VoronDesign/Voron-Legacy/STLs/Gantry/AB Drive Units/[a]_belt_tensioner_x2.stl

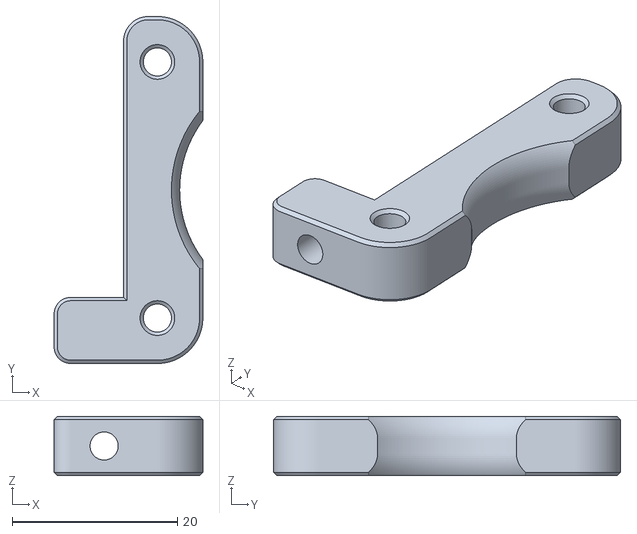
[picture p15: CAD file, 2020-12-23]
STLs/Gantry/AB Drive Units/[a]_belt_tensioner_x2.stl
18.0 x 42.0 x 7.20
