VoronDesign/Voron-Legacy/STLs/Gantry/Front Idlers/front_idler_right_upper.stl

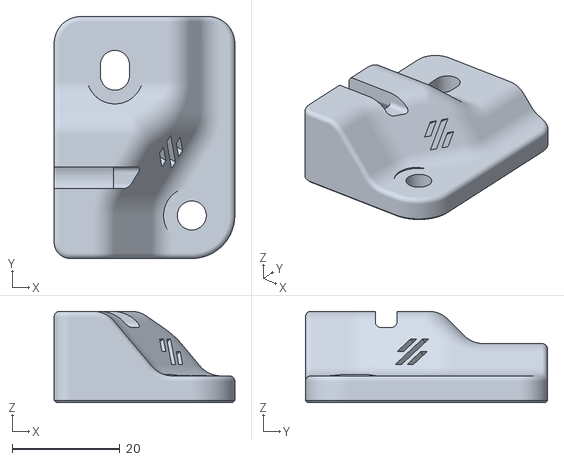
[picture p16: CAD file, 2020-12-23]
STLs/Gantry/Front Idlers/front_idler_right_upper.stl
33.6 x 45.0 x 17.0
