VoronDesign/Voron-Legacy/STLs/Gantry/X Carriage/blower_housing_rear.stl

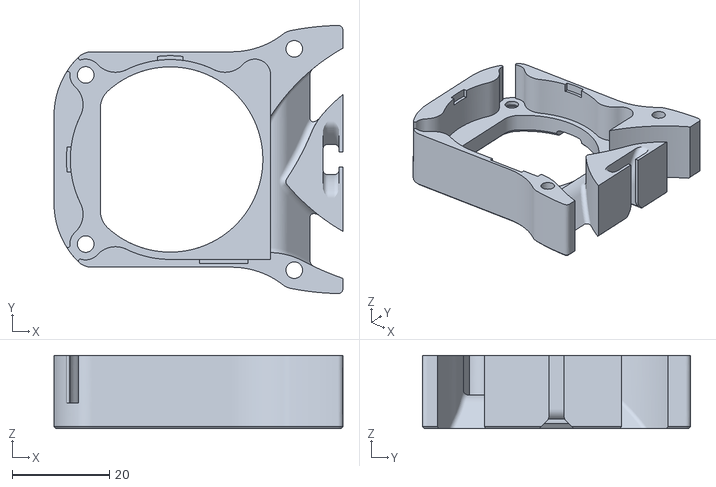
[picture p17: CAD file, 2020-12-30]
STLs/Gantry/X Carriage/blower_housing_rear.stl
59.3 x 55.0 x 15.0
