VoronDesign/Voron-Legacy/STLs/Gantry/X Carriage/Printheads/E3D V6/printhead_front_e3dv6.stl

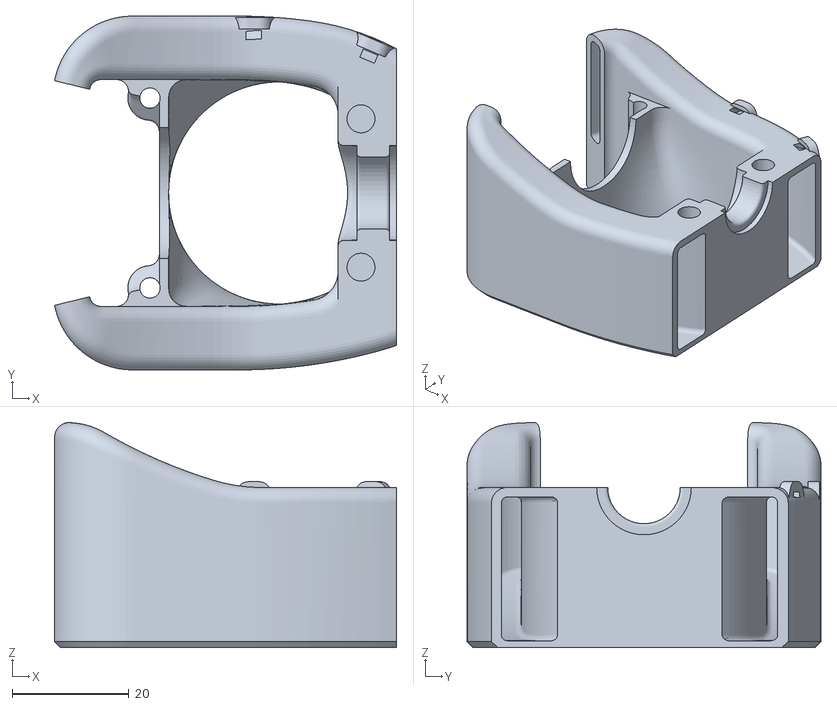
[picture p18: CAD file, 2020-12-23]
STLs/Gantry/X Carriage/Printheads/E3D V6/printhead_front_e3dv6.stl
58.6 x 60.6 x 38.5
