VoronDesign/Voron-Legacy/STLs/Gantry/X Carriage/Printheads/Slice Mosquito/printhead_rear_mosquito.stl

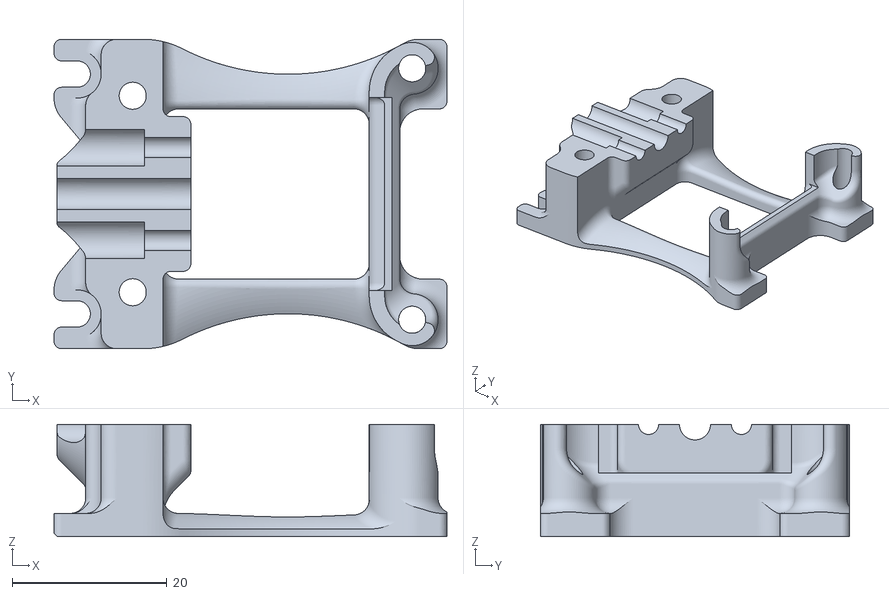
[picture p19: CAD file, 2020-12-23]
STLs/Gantry/X Carriage/Printheads/Slice Mosquito/printhead_rear_mosquito.stl
50.8 x 40.0 x 14.5
