VoronDesign/Voron-Legacy/STLs/Gantry/X Carriage/Printheads/TriangleLab Dragon/printhead_rear_dragon.stl

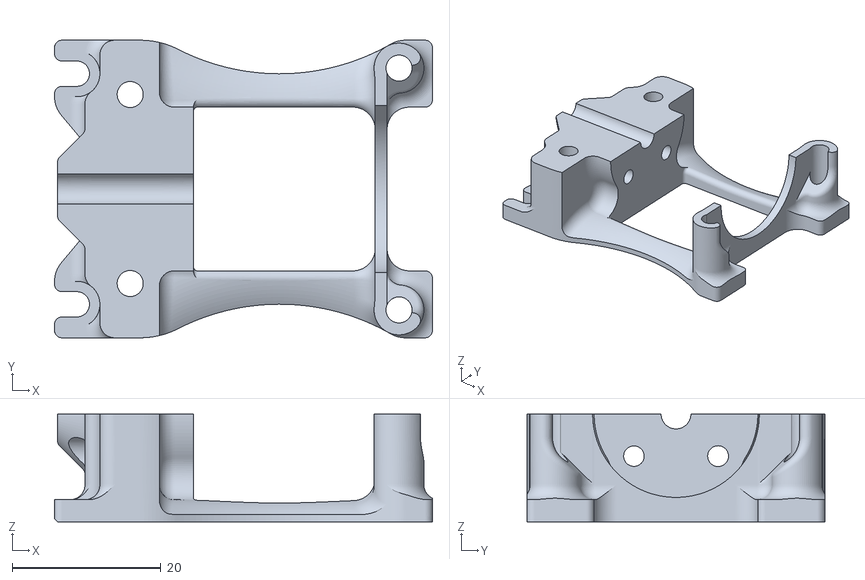
[picture p20: CAD file, 2020-12-23]
STLs/Gantry/X Carriage/Printheads/TriangleLab Dragon/printhead_rear_dragon.stl
50.8 x 40.0 x 14.5
