VoronDesign/Voron-Legacy/STLs/Gantry/XY Joints/y_bearing_retainer_front_x2.stl

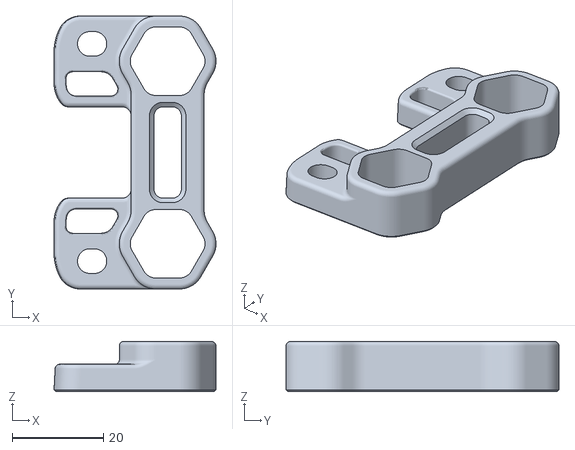
[picture p21: CAD file, 2020-12-23]
STLs/Gantry/XY Joints/y_bearing_retainer_front_x2.stl
35.5 x 59.8 x 11.0
