VoronDesign/Voron-Legacy/STLs/Tools/z_component_alignment_jig.stl

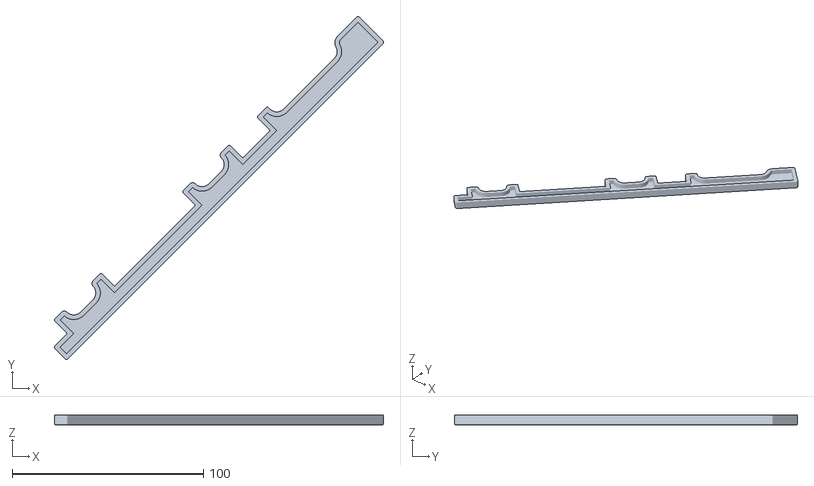
[picture p22: CAD file, 2020-12-23]
STLs/Tools/z_component_alignment_jig.stl
172.1 x 179.2 x 5.00
