VoronDesign/Voron-Legacy/STLs/Z Axis/Bed Carriages/bed_carriage_upper_b_x2.stl

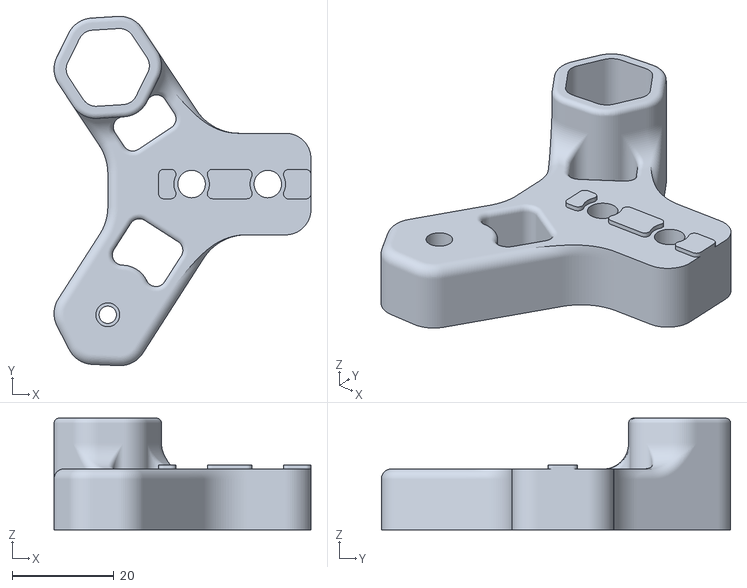
[picture p23: CAD file, 2020-12-23]
STLs/Z Axis/Bed Carriages/bed_carriage_upper_b_x2.stl
50.6 x 68.8 x 22.0
