VoronDesign/Voron-Legacy/STLs/Z Axis/z_motor_mount_b_x2.stl

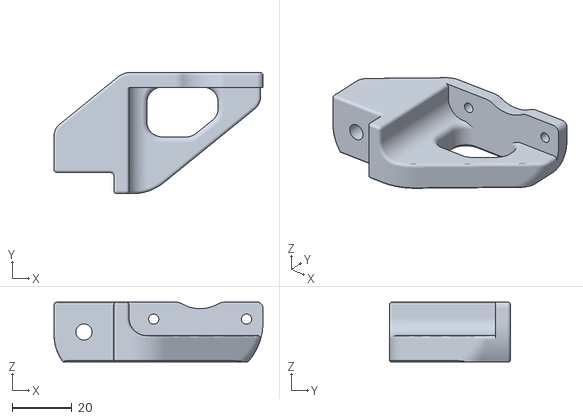
[picture p24: CAD file, 2020-12-23]
STLs/Z Axis/z_motor_mount_b_x2.stl
69.8 x 40.5 x 20.0
