VoronDesign/Voron-Legacy/STLs/Electronics/LCD/lcd_front.stl

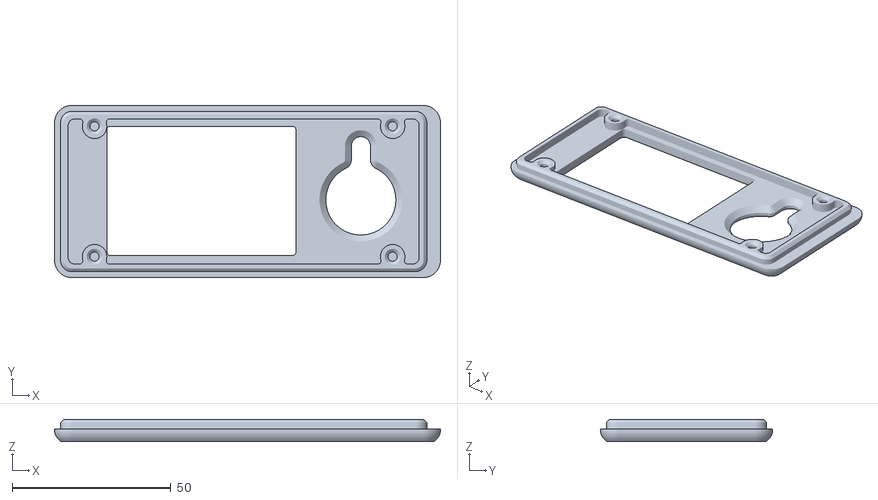
[picture p25: CAD file, 2020-12-23]
STLs/Electronics/LCD/lcd_front.stl
121.4 x 54.2 x 7.00
