VoronDesign/Voron-Legacy/STLs/Electronics/psu_stabilizer.stl

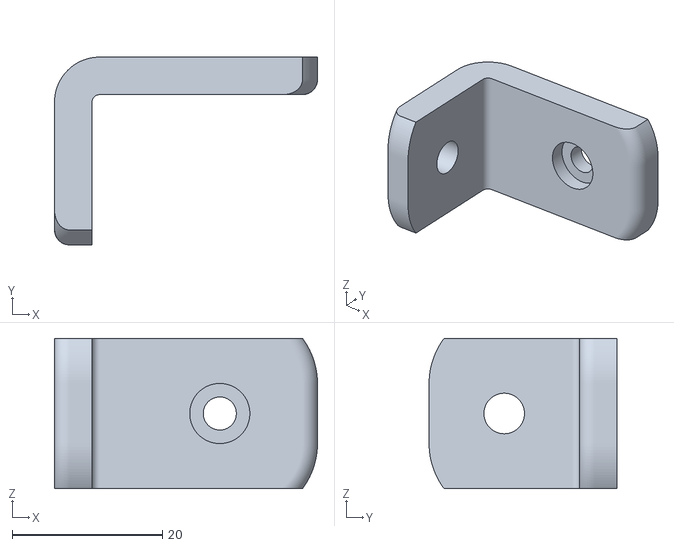
[picture p26: CAD file, 2020-12-23]
STLs/Electronics/psu_stabilizer.stl
35.0 x 25.0 x 20.0
