VoronDesign/Voron-Legacy/STLs/Gantry/X Carriage/[a]_blower_housing_front.stl

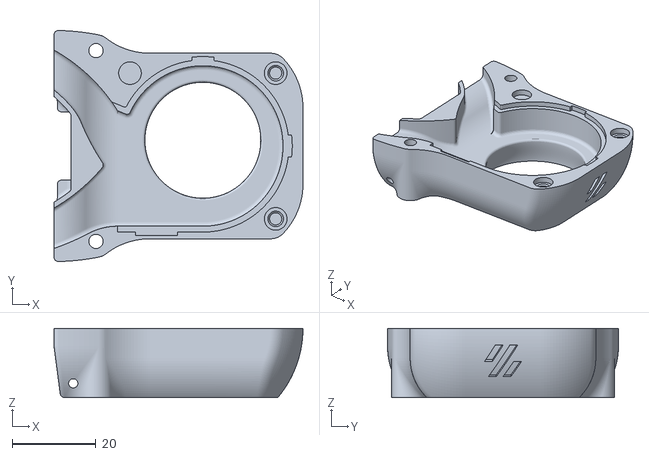
[picture p28: CAD file, 2020-12-30]
STLs/Gantry/X Carriage/[a]_blower_housing_front.stl
59.3 x 55.0 x 16.5
