VoronDesign/Voron-Legacy/STLs/Electronics/cable_frame_anchor_x10.stl

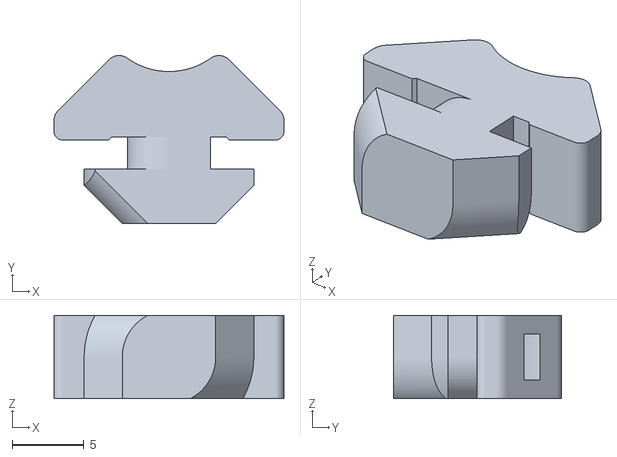
[picture p29: CAD file, 2020-12-23]
STLs/Electronics/cable_frame_anchor_x10.stl
16.0 x 11.7 x 5.80
