VoronDesign/Voron-Legacy/STLs/Electronics/LCD/lcd_mount.stl

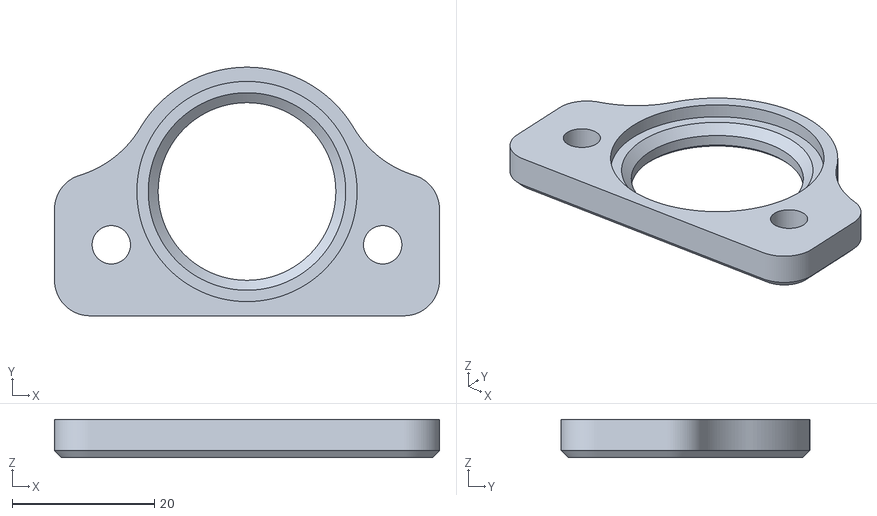
[picture p30: CAD file, 2020-12-23]
STLs/Electronics/LCD/lcd_mount.stl
54.2 x 35.0 x 5.40
