VoronDesign/Voron-Legacy/STLs/Gantry/AB Drive Units/a_drive_unit_lower.stl

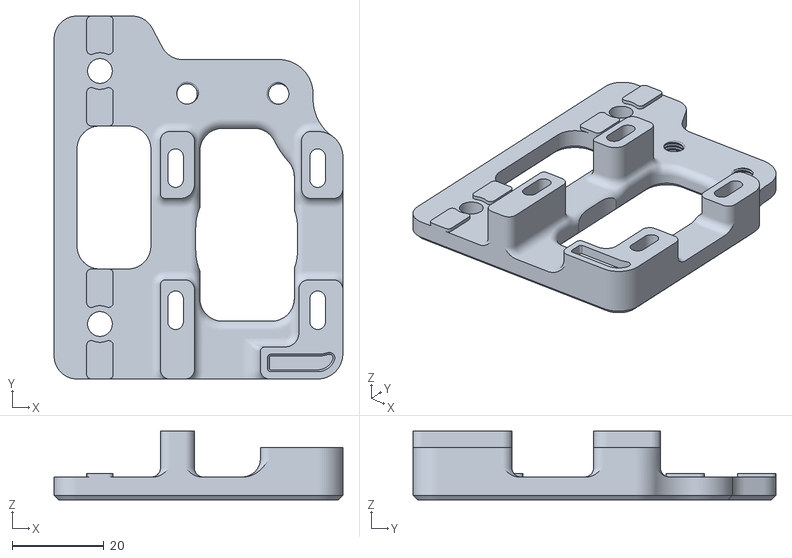
[picture p31: CAD file, 2020-12-23]
STLs/Gantry/AB Drive Units/a_drive_unit_lower.stl
63.0 x 79.2 x 15.0
