VoronDesign/Voron-Legacy/STLs/Gantry/Front Idlers/idler_spacer_x2.stl

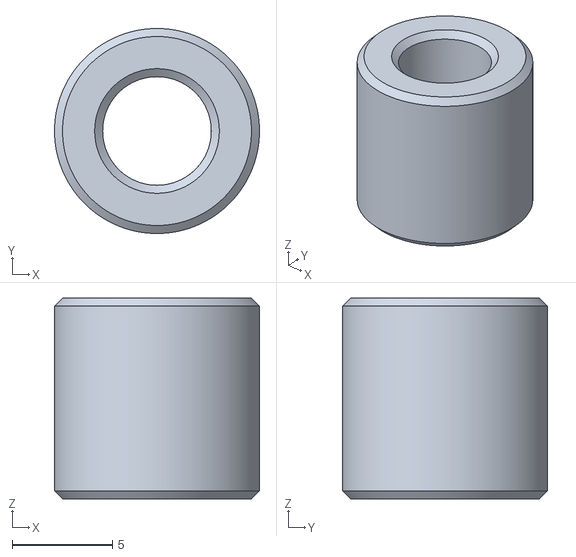
[picture p32: CAD file, 2020-12-23]
STLs/Gantry/Front Idlers/idler_spacer_x2.stl
10.2 x 10.2 x 10.0
