VoronDesign/Voron-Legacy/STLs/Gantry/X Carriage/x_carriage_right.stl

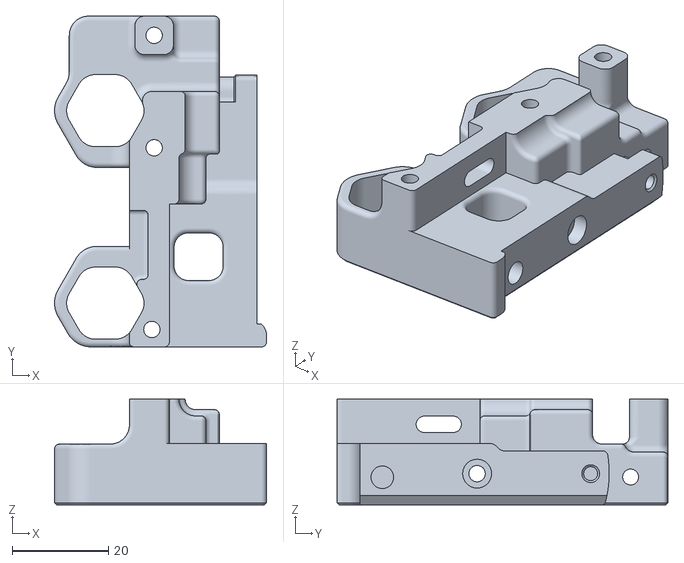
[picture p33: CAD file, 2020-12-23]
STLs/Gantry/X Carriage/x_carriage_right.stl
44.1 x 68.8 x 22.0
