VoronDesign/Voron-Legacy/STLs/Gantry/XY Joints/xy_joint_left_lower.stl

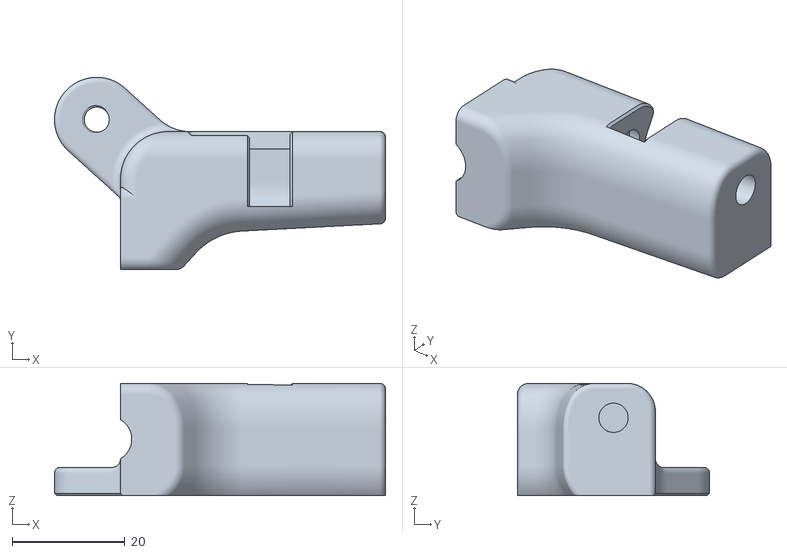
[picture p34: CAD file, 2020-12-23]
STLs/Gantry/XY Joints/xy_joint_left_lower.stl
58.7 x 34.1 x 19.9
