VoronDesign/Voron-Legacy/STLs/Z Axis/z_shaft_suport_lower_b_x2.stl

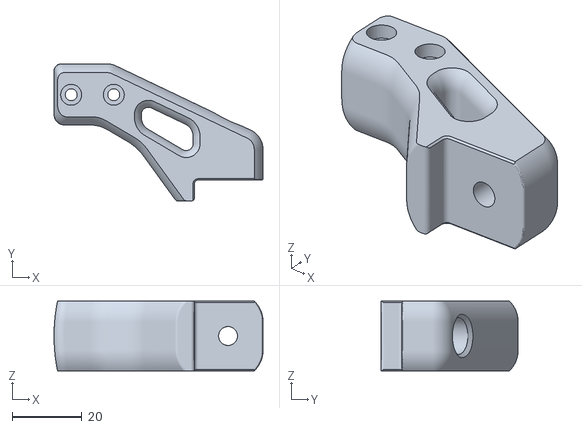
[picture p35: CAD file, 2020-12-23]
STLs/Z Axis/z_shaft_suport_lower_b_x2.stl
59.8 x 39.3 x 20.0
