VoronDesign/Voron-Legacy/STLs/Gantry/X Carriage/bowden_adapter_front.stl

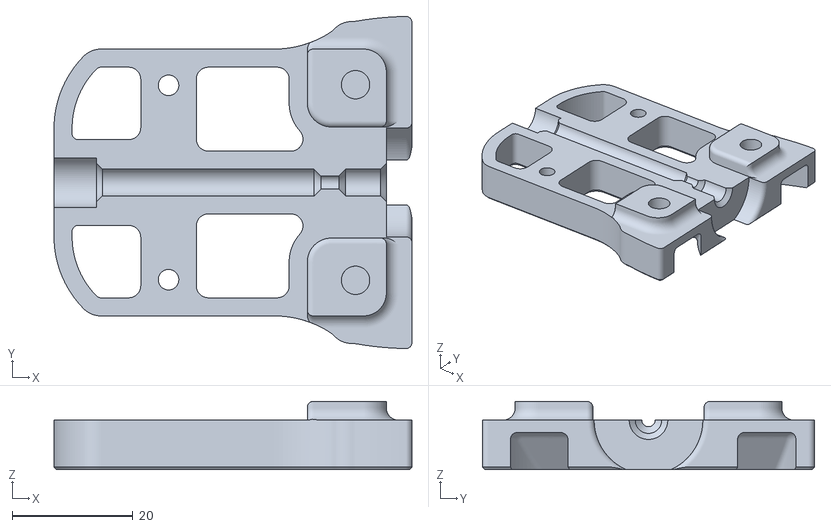
[picture p37: CAD file, 2020-12-23]
STLs/Gantry/X Carriage/bowden_adapter_front.stl
59.3 x 55.0 x 11.3
