VoronDesign/Voron-Legacy/STLs/Gantry/X Carriage/bowden_adapter_midsection.stl

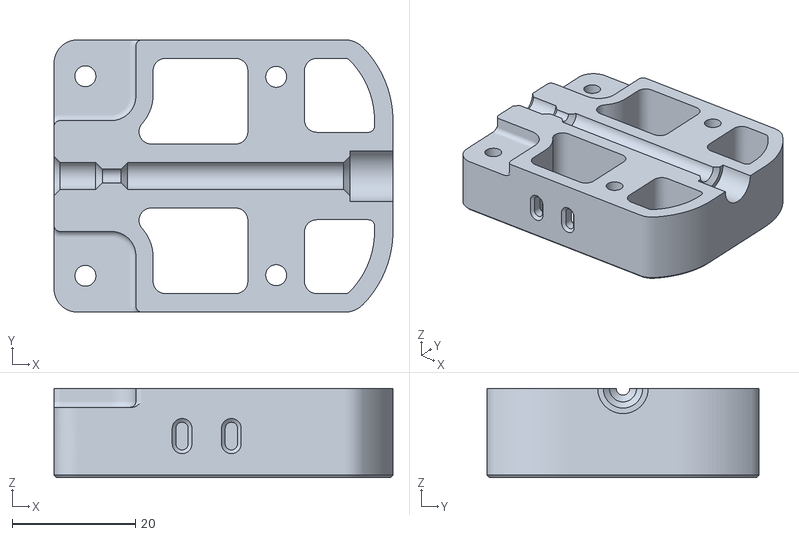
[picture p38: CAD file, 2020-12-23]
STLs/Gantry/X Carriage/bowden_adapter_midsection.stl
55.0 x 44.2 x 14.5
