VoronDesign/Voron-Legacy/STLs/Gantry/XY Joints/xy_joint_backbrace_x2.stl

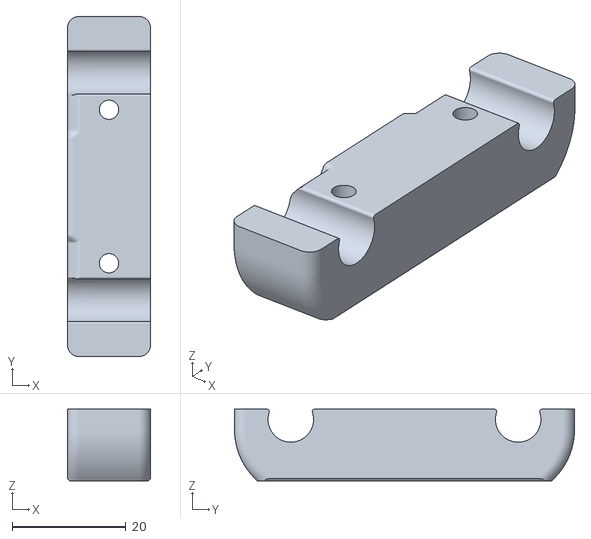
[picture p39: CAD file, 2020-12-23]
STLs/Gantry/XY Joints/xy_joint_backbrace_x2.stl
14.6 x 59.8 x 12.6
