VoronDesign/Voron-Legacy/STLs/Gantry/X Carriage/bowden_adapter_rear.stl

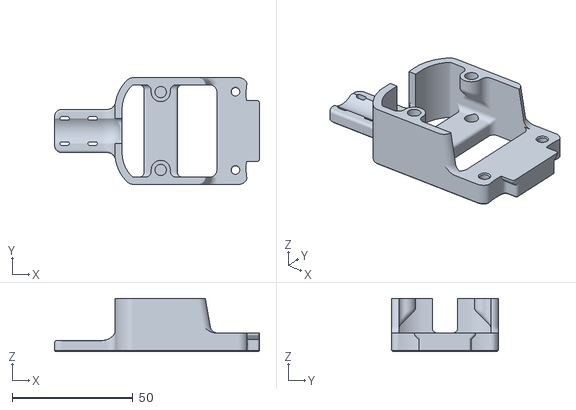
[picture p40: CAD file, 2020-12-23]
STLs/Gantry/X Carriage/bowden_adapter_rear.stl
84.9 x 44.2 x 22.0
