VoronDesign/Voron-Legacy/STLs/Gantry/XY Joints/y_bearing_retainer_rear_x2.stl

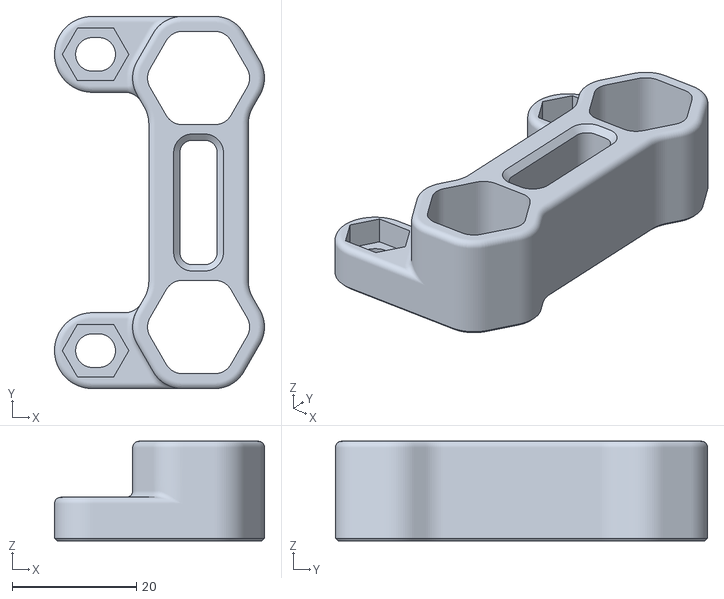
[picture p41: CAD file, 2020-12-23]
STLs/Gantry/XY Joints/y_bearing_retainer_rear_x2.stl
33.7 x 59.8 x 16.0
