VoronDesign/Voron-Legacy/STLs/Gantry/X Carriage/[a]_hotend_fan_mount.stl

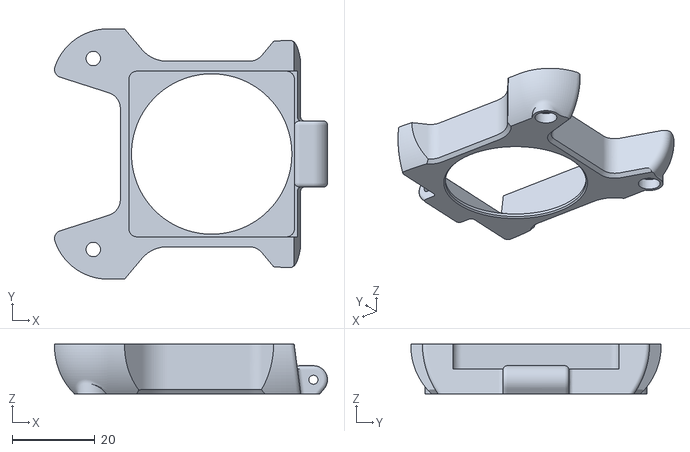
[picture p42: CAD file, 2020-12-23]
STLs/Gantry/X Carriage/[a]_hotend_fan_mount.stl
66.1 x 60.6 x 12.0
