VoronDesign/Voron-Legacy/STLs/Gantry/X Carriage/[a]_bowden_cable_cover.stl

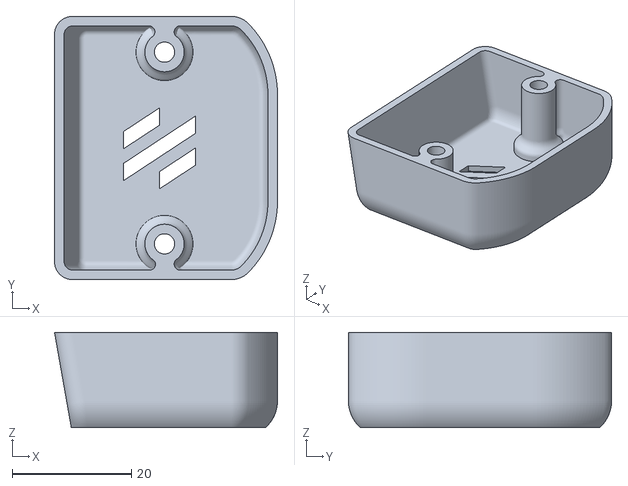
[picture p43: CAD file, 2020-12-23]
STLs/Gantry/X Carriage/[a]_bowden_cable_cover.stl
37.5 x 44.2 x 16.0
