VoronDesign/Voron-Legacy/STLs/Gantry/X Carriage/[a]_belt_clip_x2.stl

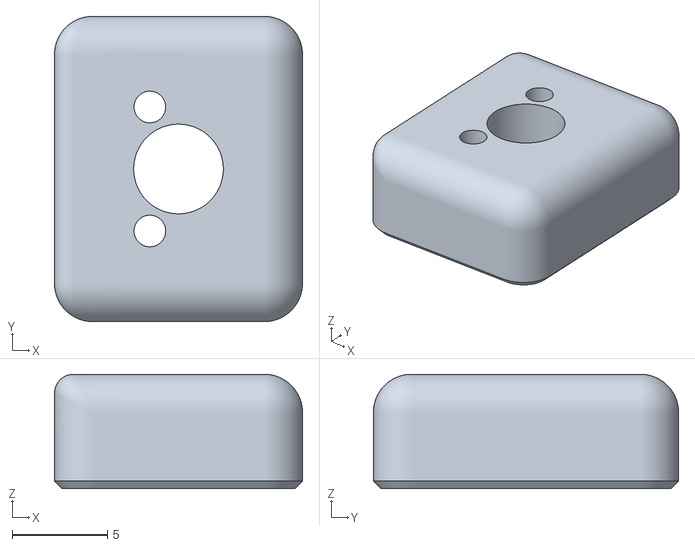
[picture p44: CAD file, 2020-12-23]
STLs/Gantry/X Carriage/[a]_belt_clip_x2.stl
13.0 x 16.0 x 6.00
