VoronDesign/Voron-Legacy/STLs/Gantry/X Carriage/probe_retainer_bracket.stl

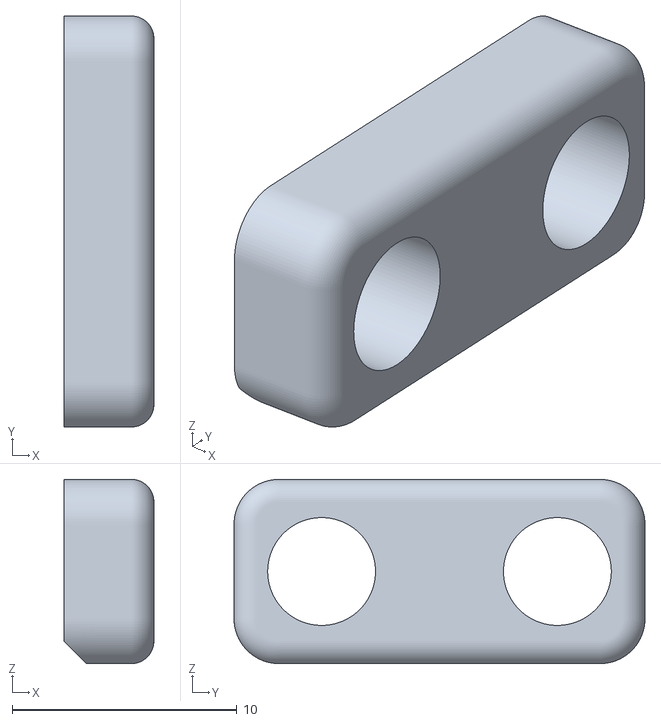
[picture p45: CAD file, 2020-12-23]
STLs/Gantry/X Carriage/probe_retainer_bracket.stl
4.00 x 18.3 x 8.20
